Kolodieiev/perfect_console/resources/images/pcb/fact_full.jpg

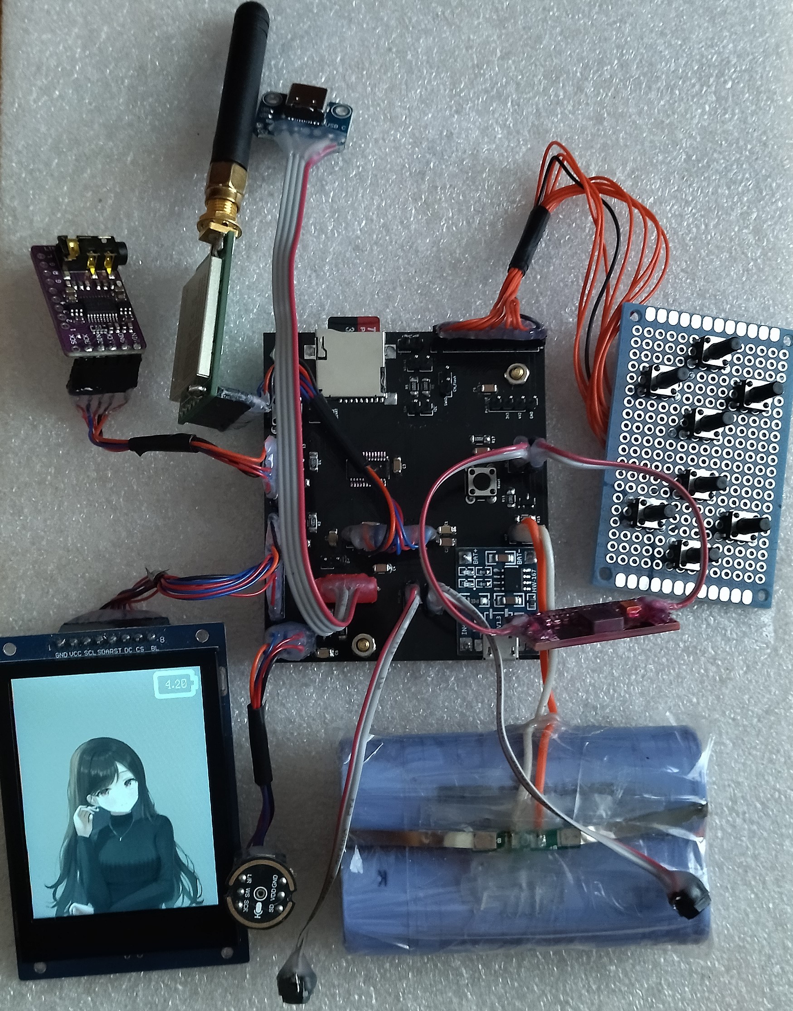
resources/images/pcb/fact_full.jpg
