Kolodieiev/perfect_console/resources/images/pcb/fact_min.jpg

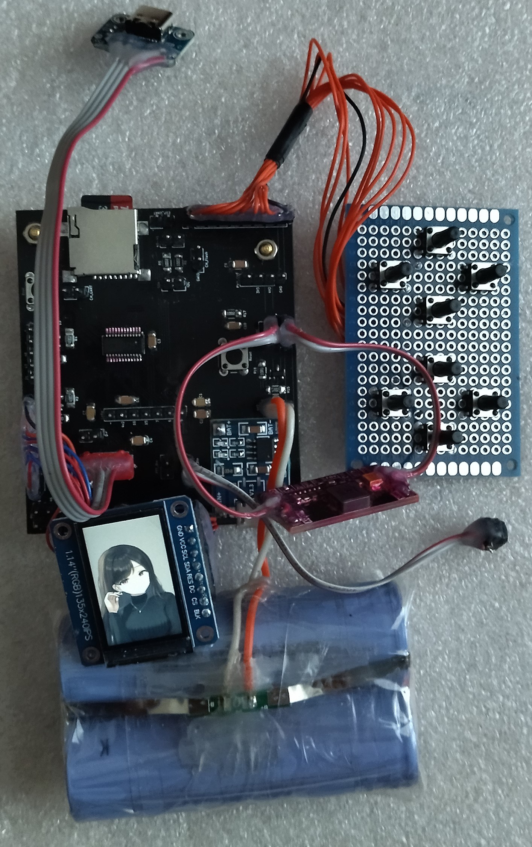
resources/images/pcb/fact_min.jpg
