Kolodieiev/perfect_console/resources/images/pcb/lpt.jpg

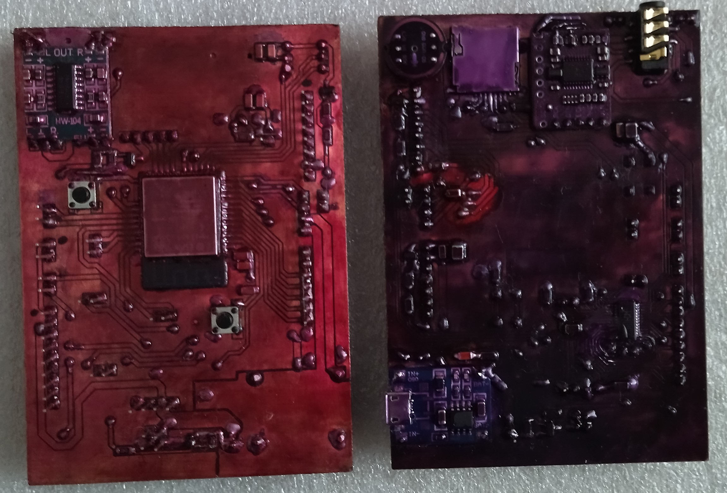
resources/images/pcb/lpt.jpg
