Kolodieiev/perfect_console/firmware/esp32s3_fw/src/pixeler/src/driver/graphics/DisplayWrapper.cpp

#pragma GCC optimize("O3")
#include "DisplayWrapper.h"

#include <esp32-hal-ledc.h>

#include <cmath>

#include "pixeler/src/manager/res/BmpLoader.h"

namespace pixeler
{
  DisplayWrapper::DisplayWrapper()
  {
  }

  DisplayWrapper::~DisplayWrapper()
  {
    log_e("Цього не повинно було статися!");
    esp_restart();
  }

  void DisplayWrapper::fillScreen(uint16_t color)
  {
#ifdef GRAPHICS_ENABLED
#ifdef DIRECT_DRAWING
    _output->fillScreen(color);
#else
    _canvas.fillScreen(color);
    _is_buff_changed = true;
#endif  // #ifdef DIRECT_DRAWING
#endif  // #ifdef GRAPHICS_ENABLED
  }

  void DisplayWrapper::setCursor(int16_t x, int16_t y)
  {
#ifdef GRAPHICS_ENABLED
#ifdef DIRECT_DRAWING
    _output->setCursor(x, y);
#else
    _canvas.setCursor(x, y);
#endif  // #ifdef DIRECT_DRAWING
#endif  // #ifdef GRAPHICS_ENABLED
  }

  void DisplayWrapper::setTextWrap(bool state)
  {
#ifdef GRAPHICS_ENABLED
#ifdef DIRECT_DRAWING
    _output->setTextWrap(state);
#else
    _canvas.setTextWrap(state);
#endif  // #ifdef DIRECT_DRAWING
#endif  // #ifdef GRAPHICS_ENABLED
  }

  void DisplayWrapper::setTextBound(int16_t x, int16_t y, int16_t w, int16_t h)
  {
#ifdef GRAPHICS_ENABLED
#ifdef DIRECT_DRAWING
    return _output->setTextBound(x, y, w, h);
#else
    _is_buff_changed = true;
    return _canvas.setTextBound(x, y, w, h);
#endif  // #ifdef DIRECT_DRAWING
#endif  // #ifdef GRAPHICS_ENABLED
  }

  void DisplayWrapper::resetTextBound()
  {
#ifdef GRAPHICS_ENABLED
#ifdef DIRECT_DRAWING
    return _output->resetTextBound();
#else
    _is_buff_changed = true;
    return _canvas.resetTextBound();
#endif  // #ifdef DIRECT_DRAWING
#endif  // #ifdef GRAPHICS_ENABLED
  }

  size_t DisplayWrapper::print(const char* str)
  {
#ifdef GRAPHICS_ENABLED
#ifdef DIRECT_DRAWING
    return _output->print(str);
#else
    _is_buff_changed = true;
    return _canvas.print(str);
#endif  // #ifdef DIRECT_DRAWING
#else   // not def GRAPHICS_ENABLED
    return 0;
#endif  // #ifdef GRAPHICS_ENABLED
  }

  void DisplayWrapper::setPPAState(bool state)
  {
#ifdef GRAPHICS_ENABLED
    _canvas.setPPAState(state);
#endif  // #ifdef GRAPHICS_ENABLED
  }

  bool DisplayWrapper::isPPAEnabled() const
  {
#ifdef GRAPHICS_ENABLED
    return _canvas.isPPAEnabled();
#else
    return false;
#endif  // #ifdef GRAPHICS_ENABLED
  }

  void DisplayWrapper::setFont(const uint8_t* font)
  {
#ifdef GRAPHICS_ENABLED
#ifdef DIRECT_DRAWING
    _output->setFont(font);
#else
    _canvas.setFont(font);
#endif  // #ifdef DIRECT_DRAWING
#endif  // #ifdef GRAPHICS_ENABLED
  }

  void DisplayWrapper::setTextSize(uint8_t size)
  {
#ifdef GRAPHICS_ENABLED
#ifdef DIRECT_DRAWING
    _output->setTextSize(size, size, 0);
#else
    _canvas.setTextSize(size, size, 0);
#endif  // #ifdef DIRECT_DRAWING
#endif  // #ifdef GRAPHICS_ENABLED
  }

  void DisplayWrapper::setTextColor(uint16_t color)
  {
#ifdef GRAPHICS_ENABLED
#ifdef DIRECT_DRAWING
    _output->setTextColor(color);
#else
    _canvas.setTextColor(color);
#endif  // #ifdef DIRECT_DRAWING
#endif  // #ifdef GRAPHICS_ENABLED
  }

  void DisplayWrapper::calcTextBounds(const char* str, int16_t x, int16_t y, int16_t& x_out, int16_t& y_out, uint16_t& w_out, uint16_t& h_out)
  {
#ifdef GRAPHICS_ENABLED
#ifdef DIRECT_DRAWING
    _output->getTextBounds(str, x, y, x_out, y_out, w_out, h_out);
#else
    _canvas.getTextBounds(str, x, y, x_out, y_out, w_out, h_out);
#endif  // #ifdef DIRECT_DRAWING
#endif  // #ifdef GRAPHICS_ENABLED
  }

  void DisplayWrapper::drawPixel(int16_t x, int16_t y, uint16_t color)
  {
#ifdef GRAPHICS_ENABLED
#ifdef DIRECT_DRAWING
    _output->drawPixel(x, y, color);
#else
    _canvas.drawPixel(x, y, color);
    _is_buff_changed = true;
#endif  // #ifdef DIRECT_DRAWING
#endif  // #ifdef GRAPHICS_ENABLED
  }

  void DisplayWrapper::drawLine(int16_t x0, int16_t y0, int16_t x1, int16_t y1, uint16_t color)
  {
#ifdef GRAPHICS_ENABLED
#ifdef DIRECT_DRAWING
    _output->drawLine(x0, y0, x1, y1, color);
#else
    _canvas.drawLine(x0, y0, x1, y1, color);
    _is_buff_changed = true;
#endif  // #ifdef DIRECT_DRAWING
#endif  // #ifdef GRAPHICS_ENABLED
  }

  void DisplayWrapper::drawCircle(int16_t x, int16_t y, int16_t r, uint16_t color)
  {
#ifdef GRAPHICS_ENABLED
#ifdef DIRECT_DRAWING
    _output->drawCircle(x, y, r, color);
#else
    _canvas.drawCircle(x, y, r, color);
    _is_buff_changed = true;
#endif  // #ifdef DIRECT_DRAWING
#endif  // #ifdef GRAPHICS_ENABLED
  }

  void DisplayWrapper::fillCircle(int16_t x, int16_t y, int16_t r, uint16_t color)
  {
#ifdef GRAPHICS_ENABLED
#ifdef DIRECT_DRAWING
    _output->fillCircle(x, y, r, color);
#else
    _canvas.fillCircle(x, y, r, color);
    _is_buff_changed = true;
#endif  // #ifdef DIRECT_DRAWING
#endif  // #ifdef GRAPHICS_ENABLED
  }

  void DisplayWrapper::drawRect(int32_t x, int32_t y, int32_t w, int32_t h, uint16_t color)
  {
#ifdef GRAPHICS_ENABLED
#ifdef DIRECT_DRAWING
    _output->drawRect(x, y, w, h, color);
#else
    _canvas.drawRect(x, y, w, h, color);
    _is_buff_changed = true;
#endif  // #ifdef DIRECT_DRAWING
#endif  // #ifdef GRAPHICS_ENABLED
  }

  void DisplayWrapper::fillRect(int32_t x, int32_t y, int32_t w, int32_t h, uint16_t color)
  {
#ifdef GRAPHICS_ENABLED
#ifdef DIRECT_DRAWING
    _output->fillRect(x, y, w, h, color);
#else
    _canvas.fillRect(x, y, w, h, color);
    _is_buff_changed = true;
#endif  // #ifdef DIRECT_DRAWING
#endif  // #ifdef GRAPHICS_ENABLED
  }

  void DisplayWrapper::drawRoundRect(int32_t x, int32_t y, int32_t w, int32_t h, int32_t radius, uint16_t color)
  {
#ifdef GRAPHICS_ENABLED
#ifdef DIRECT_DRAWING
    _output->drawRoundRect(x, y, w, h, radius, color);
#else
    _canvas.drawRoundRect(x, y, w, h, radius, color);
    _is_buff_changed = true;
#endif  // #ifdef DIRECT_DRAWING
#endif  // #ifdef GRAPHICS_ENABLED
  }

  void DisplayWrapper::fillRoundRect(int32_t x, int32_t y, int32_t w, int32_t h, int32_t radius, uint16_t color)
  {
#ifdef GRAPHICS_ENABLED
#ifdef DIRECT_DRAWING
    _output->fillRoundRect(x, y, w, h, radius, color);
#else
    _canvas.fillRoundRect(x, y, w, h, radius, color);
    _is_buff_changed = true;
#endif  // #ifdef DIRECT_DRAWING
#endif  // #ifdef GRAPHICS_ENABLED
  }

  void DisplayWrapper::drawBitmap(int16_t x, int16_t y, const uint16_t* bitmap, int16_t w, int16_t h)
  {
#ifdef GRAPHICS_ENABLED
#ifdef DIRECT_DRAWING
    _output->draw16bitRGBBitmap(x, y, bitmap, w, h);
#else
    _canvas.draw16bitRGBBitmap(x, y, bitmap, w, h);
    _is_buff_changed = true;
#endif  // #ifdef DIRECT_DRAWING
#endif  // #ifdef GRAPHICS_ENABLED
  }

  void DisplayWrapper::drawBitmapTransp(int16_t x, int16_t y, const uint16_t* bitmap, int16_t w, int16_t h)
  {
#ifdef GRAPHICS_ENABLED
#ifdef DIRECT_DRAWING
    _output->draw16bitRGBBitmapWithTranColor(x, y, bitmap, COLOR_TRANSPARENT, w, h);
#else
    _canvas.draw16bitRGBBitmapWithTranColor(x, y, bitmap, COLOR_TRANSPARENT, w, h);
    _is_buff_changed = true;
#endif  // #ifdef DIRECT_DRAWING
#endif  // #ifdef GRAPHICS_ENABLED
  }

  void DisplayWrapper::drawBitmapRotated(int16_t x, int16_t y, const uint16_t* bitmap, int16_t w, int16_t h, float piv_x, float piv_y, float angle)
  {
#ifdef GRAPHICS_ENABLED
#ifndef DIRECT_DRAWING
    const float rad = angle * (M_PI / 180.0f);
    const float cos_a = cosf(rad);
    const float sin_a = sinf(rad);

    uint16_t* rotated = static_cast<uint16_t*>(ps_malloc(w * h * sizeof(uint16_t)));
    if (!rotated)
    {
      log_e("Memory allocation failed");
      esp_restart();
    }

    for (int i = 0; i < w * h; i++)
      rotated[i] = COLOR_TRANSPARENT;

    for (int16_t dst_y = 0; dst_y < h; dst_y++)
    {
      const float rel_y = static_cast<float>(dst_y) - piv_y + 0.5f;
      const float y_cos = rel_y * cos_a;
      const float y_sin = rel_y * sin_a;

      for (int16_t dst_x = 0; dst_x < w; dst_x++)
      {
        const float rel_x = static_cast<float>(dst_x) - piv_x + 0.5f;

        const int16_t src_x = static_cast<int16_t>(rel_x * cos_a + y_sin + piv_x);
        const int16_t src_y = static_cast<int16_t>(-rel_x * sin_a + y_cos + piv_y);

        if (src_x >= 0 && src_x < w && src_y >= 0 && src_y < h)
          rotated[dst_y * w + dst_x] = bitmap[src_y * w + src_x];
      }
    }

    _canvas.draw16bitRGBBitmapWithTranColor(x, y, rotated, COLOR_TRANSPARENT, w, h);
    delete[] rotated;
#endif  // #ifndef DIRECT_DRAWING
#endif  // #ifdef GRAPHICS_ENABLED
  }

  uint16_t DisplayWrapper::getFontHeight(const uint8_t* font, uint8_t size)
  {
#ifdef GRAPHICS_ENABLED
    int16_t x1, y1;
    uint16_t w, h;
    _display.setTextSize(size);
    _display.setFont(font);
    _display.calcTextBounds("Ґg", 0, 0, x1, y1, w, h);
    return h;
#else   // not def GRAPHICS_ENABLED
    return 0;
#endif  // #ifdef GRAPHICS_ENABLED
  }

  SemaphoreHandle_t DisplayWrapper::getMutex()
  {
#ifdef GRAPHICS_ENABLED
#ifdef DIRECT_DRAWING
    return nullptr;
#else
    return _sync_mutex;
#endif  // #ifdef DIRECT_DRAWING
#else   // not def GRAPHICS_ENABLED
    return nullptr;
#endif  // #ifdef GRAPHICS_ENABLED
  }

  void DisplayWrapper::rotateDisplaySquare(uint16_t x, uint16_t y, uint16_t side_len, RotateAngle angle)
  {
#ifdef GRAPHICS_ENABLED
#ifndef DIRECT_DRAWING
    side_len = std::min<uint16_t>(side_len, std::min(UI_WIDTH, UI_HEIGHT));
    uint16_t* display_buff = static_cast<uint16_t*>(_canvas.getFramebuffer());
    const size_t square_img_size = side_len * side_len * sizeof(uint16_t);

    uint16_t* square_img = static_cast<uint16_t*>(ps_malloc(square_img_size));
    if (!square_img)
    {
      log_e("Memory allocation failed");
      esp_restart();
    }

    const uint16_t canvas_w = _canvas.width();
    const uint16_t canvas_h = _canvas.height();

    for (uint16_t row = 0; row < side_len; row++)
    {
      uint16_t* src_row_ptr = &display_buff[(y + row) * canvas_w + x];
      uint16_t* dst_row_ptr = &square_img[row * side_len];
      memcpy(dst_row_ptr, src_row_ptr, side_len * sizeof(uint16_t));
    }

    bool old_ppa_state = _canvas.isPPAEnabled();
    if (side_len * side_len > PPA_IMG_SIZE_TRIGG)
      _canvas.setPPAState(true);

    switch (angle)
    {
      case ROTATE_ANGLE_90:
        _canvas.drawBitmapToFramebufferRotate1(square_img, side_len, side_len, display_buff, x, y, canvas_w, canvas_h);
        break;
      case ROTATE_ANGLE_180:
        _canvas.drawBitmapToFramebufferRotate2(square_img, side_len, side_len, display_buff, x, y, canvas_w, canvas_h);
        break;
      case ROTATE_ANGLE_270:
        _canvas.drawBitmapToFramebufferRotate3(square_img, side_len, side_len, display_buff, x, y, canvas_w, canvas_h);
        break;
    }
    _canvas.setPPAState(old_ppa_state);
    free(square_img);
#endif  // #ifdef DIRECT_DRAWING
#endif  // #ifdef GRAPHICS_ENABLED
  }

  void DisplayWrapper::__init()
  {
#ifdef GRAPHICS_ENABLED
    if (BUSS_FREQUENCY < 10000000)
    {
      log_e("Встановлено занадто низьку швидкість шини");
      esp_restart();
    }

#ifdef DIRECT_DRAWING
    _output->begin(BUSS_FREQUENCY);
    _output->setUTF8Print(true);
    _output->setTextWrap(false);
#else
    _canvas.begin(BUSS_FREQUENCY);
    _canvas.setUTF8Print(true);
    _canvas.setTextWrap(false);
#endif  // #ifdef DIRECT_DRAWING

#ifdef INVERT_COLORS
    _output->invertDisplay(INVERT_COLORS);
#endif  //  #ifdef INVERT_COLORS

    _output->setRotation(DISPLAY_ROTATION);

#if ROTATE_CANVAS
    _canvas.setRotation(DISPLAY_ROTATION);
#endif  // #if ROTATE_CANVAS

    _sync_mutex = xSemaphoreCreateMutex();

    if (!_sync_mutex)
    {
      log_e("Недостатньо ресурсів для роботи графічного драйвера");
      esp_restart();
    }

#ifdef DOUBLE_BUFFERRING
    BaseType_t result = xTaskCreatePinnedToCore(displayRendererTask, "dRend", 5 * 512, this, 11, nullptr, 0);

    if (result != pdPASS)
    {
      log_e("Недостатньо ресурсів для роботи графічного драйвера");
      esp_restart();
    }
#endif  // DOUBLE_BUFFERRING
#endif  // #ifdef GRAPHICS_ENABLED
  }

#ifdef ENABLE_SCREENSHOTER
  void DisplayWrapper::takeScreenshot()
  {
    _take_screenshot = true;
    _is_buff_changed = true;
  }
#endif  // ENABLE_SCREENSHOTER

#ifdef PIN_DISPLAY_BL
  void DisplayWrapper::enableBackLight()
  {
#ifdef HAS_BL_PWM
    ledcAttach(PIN_DISPLAY_BL, DISPLAY_BL_PWM_FREQ, DISPLAY_BL_PWM_RES);
    ledcWrite(PIN_DISPLAY_BL, _cur_brightness);
#else
    pinMode(PIN_DISPLAY_BL, OUTPUT);
    digitalWrite(PIN_DISPLAY_BL, HIGH);
#endif  // HAS_BL_PWM
  }

  void DisplayWrapper::disableBackLight()
  {
#ifdef HAS_BL_PWM
    ledcDetach(PIN_DISPLAY_BL);
#endif  // HAS_BL_PWM
    digitalWrite(PIN_DISPLAY_BL, LOW);
  }

#ifdef HAS_BL_PWM
  void DisplayWrapper::setBrightness(uint8_t value)
  {
    if (value == 0)
      fillScreen(COLOR_BLACK);

    _cur_brightness = value;
    ledcWrite(PIN_DISPLAY_BL, value);
  }

  uint8_t DisplayWrapper::getBrightness() const
  {
    return _cur_brightness;
  }
#endif  // HAS_BL_PWM
#endif  // PIN_DISPLAY_BL

#ifdef GRAPHICS_ENABLED
#ifndef DIRECT_DRAWING
  void DisplayWrapper::__flush()
  {
    if (_is_buff_changed)
    {
      _is_buff_changed = false;

#ifdef SHOW_FPS
      if (millis() - _frame_timer < 1000)
      {
        ++_temp_frame_counter;
      }
      else
      {
        _frame_counter = _temp_frame_counter + 1;
        _temp_frame_counter = 0;
        _frame_timer = millis();
      }

      String fps_str = String(_frame_counter);

      _canvas.setTextSize(1);
      _canvas.setFont(font_unifont);
      _canvas.setTextColor(COLOR_RED);

      int16_t x{0};
      int16_t y{0};
      int16_t x_out{0};
      int16_t y_out{0};
      uint16_t w{0};
      uint16_t h{0};

      _canvas.getTextBounds(fps_str.c_str(), x, y, x_out, y_out, w, h);
      //
      uint16_t fps_x_pos = _canvas.width() / 2 - w;
      _canvas.fillRect(fps_x_pos - 3, 0, w + 6, h + 9, COLOR_BLACK);
      _canvas.setCursor(fps_x_pos, h + 3);
      _canvas.print(fps_str);
#endif  // SHOW_FPS

      xSemaphoreTake(_sync_mutex, portMAX_DELAY);
#ifdef DOUBLE_BUFFERRING
      _has_frame = true;
      _canvas.duplicateMainBuff();
#else
      _canvas.flushMainBuff();
#endif  // DOUBLE_BUFFERRING
      xSemaphoreGive(_sync_mutex);

#ifdef ENABLE_SCREENSHOTER
      if (_take_screenshot)
        takeScreenshot(this);
#endif  // ENABLE_SCREENSHOTER
    }
  }
#endif  // #ifndef DIRECT_DRAWING
#endif  // #ifdef GRAPHICS_ENABLED

#ifdef DOUBLE_BUFFERRING
  void DisplayWrapper::displayRendererTask(void* params)
  {
    DisplayWrapper& self = *static_cast<DisplayWrapper*>(params);

    while (1)
    {
      if (self._has_frame)
      {
        xSemaphoreTake(self._sync_mutex, portMAX_DELAY);

        self._has_frame = false;
        self._canvas.flushSecondBuff();

        xSemaphoreGive(self._sync_mutex);
      }
      delay(1);
    }
  }
#endif  // DOUBLE_BUFFERRING

#ifdef ENABLE_SCREENSHOTER
  void DisplayWrapper::takeScreenshot(DisplayWrapper* self)
  {
    self->_take_screenshot = false;

    BmpHeader header;
    header.width = self->_canvas.width();
    header.height = self->_canvas.height();

    String path_to_bmp = "/screenshot_";
    path_to_bmp += millis();
    path_to_bmp += ".bmp";

    BmpLoader loader;
    bool res = loader.saveBmp(header,
                              self->_canvas.getFramebuffer(),
                              path_to_bmp.c_str(),
                              true);

    if (res)
      log_i("Скріншот %s успішно збережено", path_to_bmp.c_str());
    else
      log_e("Помилка створення скріншоту");
  }
#endif  // ENABLE_SCREENSHOTER

  DisplayWrapper _display;
}  // namespace pixeler
