Kolodieiev/perfect_console/firmware/esp32s3_fw/src/pixeler/src/manager/WiFiManager.h

/**
 * @file WiFiManager.h
 * @brief Абстракція над бібліотекою WiFi
 * @details Покращує асинхронну взаємодію з модулем WiFi.
 * Зменшує дублювання часто використовуваного коду.
 */

#pragma once
#pragma GCC optimize("O3")
#include <WiFi.h>

#include <vector>

#include "pixeler/src/defines.h"

namespace pixeler
{
  const char STR_ROUTER_NOT_CONNECTED[] = "Не підключено до маршрутизатора";

  typedef std::function<void(void* arg, wl_status_t conn_status)> WiFiConnectDoneHandler;
  typedef std::function<void(void* arg)> WiFiScanDoneHandler;

  class WiFiManager
  {
  public:
    enum WiFiPowerLevel : uint8_t
    {
      WIFI_POWER_MIN = 0,
      WIFI_POWER_MEDIUM,
      WIFI_POWER_MAX,
    };

    /**
     * @brief Запускає асинхронну спробу підключення до точки доступу із заданими параметрами.
     *
     * @param ssid Ім'я точки доступу.
     * @param pwd Пароль точки доступу.
     * @param wifi_chan Канал WiFi.
     * @param autoreconnect Прапор, що вказує, чи потрібно виконувати автоматичну повторну спробу підключення
     * до точки доступу у разі невдачі або втрати з'єднання.
     * @return true - Якщо запуск спроби підключення виконано успішно.
     * @return false - Якщо не вдалося розпочати підключення.
     */
    bool tryConnectTo(const String& ssid, const String& pwd, uint8_t wifi_chan = 1, bool autoreconnect = false);

    /**
     * @brief Створює точку доступу WiFi, до якої можуть приєднуватися WiFi-клієнти.
     *
     * @param ssid Ім'я точки доступу.
     * @param pwd Пароль точки доступу.
     * @param max_connection Максимальна кількість підключень (більше 0, але менше 10).
     * Рекомендується встановлювати менше 5 одночасних підключень.
     * @param wifi_chan Канал WiFi (менше 11).
     * @param is_hidden Якщо true - точку доступу буде створено прихованою.
     * @return true - Якщо точка доступу створена успішно.
     * @return false - Інакше.
     */
    bool createAP(const String& ssid, const String& pwd, uint8_t max_connection = 1, uint8_t wifi_chan = 1, bool is_hidden = false);

    /**
     * @brief Встановлює обробник події, який буде викликано після завершення спроби підключення до точки доступу.
     *
     * @param handler Асинхронний обробник події завершення спроби підключення до точки доступу.
     * @param args Аргументи, що будуть передані обробнику.
     */
    void setConnectDoneHandler(WiFiConnectDoneHandler handler, void* arg);

    /**
     * @brief Встановлює обробник події, який буде викликано після завершення сканування точок WiFi.
     *
     * @param handler Асинхронний обробник події завершення сканування.
     * @param args Аргументи, що будуть передані обробнику.
     */
    void setScanDoneHandler(WiFiScanDoneHandler handler, void* arg);

    /**
     * @brief Налаштовує WiFi модуль та запускає сканування точок доступу.
     *
     * @return true - Якщо сканування було запущено.
     * @return false - Інакше.
     */
    bool startScan();

    /**
     * @brief Наповнює вектор іменами всіх виявлених точок доступу.
     * Після формування вектора, результат сканування очищується.
     *
     */
    void getScanResult(std::vector<String>& out_vector) const;

    /**
     * @brief Очищує результат попереднього сканування точок доступу.
     *
     */
    void clearScanResult();

    /**
     * @brief Встановлює потужність модуля WiFi.
     *
     * @param power_lvl Значення перечислення потужності модуля.
     * WIFI_POWER_MIN == 5 dBm.
     * WIFI_POWER_MEDIUM == 15 dBm.
     * WIFI_POWER_MAX == 19.5 dBm.
     */
    void setPower(WiFiPowerLevel power_lvl);

    /**
     * @brief Повертає логічне значення, яке вказує на те, чи встановлено з'єднання з WiFi.
     *
     * @return true - Якщо з'єднання встановлено.
     * @return false - Інакше.
     */
    bool isConnected() const;

    /**
     * @brief Повертає логічне значення, яке вказує на те, чи активовано точку доступу на пристрої.
     *
     * @return true - Якщо точка доступу активна.
     * @return false - Інакше.
     */
    bool isApEnabled() const;

    /**
     * @brief Повертає назву WiFi-точки доступу, з якою встановлено з'єднання.
     *
     * @return String - SSID точки доступу, якщо з'єднання існує, або порожній рядок, якщо з'єднання відсутнє.
     */
    String getSSID() const;

    /**
     * @brief Відключається від точки доступу, якщо було встановлено з'єднання.
     *
     */
    void disconnect();

    /**
     * @brief Повертає стан модуля WiFi.
     *
     * @return true - Якщо модуль WiFi увімкнено.
     * @return false - Інакше.
     */
    bool isEnabled() const;

    /**
     * @brief Подає сигнал увімкнення на модуль WiFi.
     *
     * @return true - Якщо модуль WiFi було успішно увімкнено.
     * @return false - Інакше.
     */
    bool enable();

    /**
     * @brief Відключається від точки доступу, якщо було встановлено з'єднання, та вимикає модуль WiFi.
     *
     */
    void disable();

    /**
     * @brief Перемикає поточний стан модуля WiFi на протилежний.
     *
     * @return true - Якщо операцію виконано успішно.
     * @return false - Інакше.
     */
    bool toggle();

    /**
     * @brief Повертає IP-адресу пристрою.
     *
     * @return String - IP-адреса пристрою, якщо пристрій знаходиться в мережі.
     * @return Порожній рядок - інакше.
     */
    String getIP();

    /**
     * @brief Повертає стан прапору, який вказує на те, чи зайнятий зараз модуль WiFi асинхронною роботою на кшталт скануваня чи підключення.
     *
     * @return true - Якщо модуль зайнятий.
     * @return false - Інакше.
     */
    bool isBusy() const;

    WiFiManager() {}
    WiFiManager(const WiFiManager&) = delete;
    WiFiManager& operator=(const WiFiManager&) = delete;
    WiFiManager(WiFiManager&&) = delete;
    WiFiManager& operator=(WiFiManager&&) = delete;

  private:
    void callConnDoneHandler();
    void callScanDoneHandler();

    static void onEvent(WiFiEvent_t event);

  private:
    WiFiScanDoneHandler _scan_done_handler{nullptr};
    WiFiConnectDoneHandler _conn_done_handler{nullptr};

    void* _scan_done_handler_arg{nullptr};
    void* _conn_done_handler_arg{nullptr};

    bool _is_busy{false};
  };

  /**
   * @brief Глобальний об'єкт для роботи з модулем WiFi.
   *
   */
  extern WiFiManager _wifi;
}  // namespace pixeler
