Kolodieiev/perfect_console/firmware/esp32s3_fw/src/pixeler/setup/i2s_setup.h

/**
 * @file i2s_setup.h
 * @brief Файл налаштувань шини I2S
 * @details Якщо цифровий мікрофон або звукову карту не підключено, визначення пінів можна залишити як є.
 */

#pragma once
#include <stdint.h>

#if defined(CONFIG_IDF_TARGET_ESP32S3)

// Піни до яких підключено модуль звукової карти.
#define PIN_I2S_OUT_BCLK 21
#define PIN_I2S_OUT_LRC 48
#define PIN_I2S_OUT_DOUT 47

// Піни до яких підключено цифровий мікрофон.
#define PIN_I2S_IN_SCK 3
#define PIN_I2S_IN_WS 46
#define PIN_I2S_IN_SD 9

#else

#define PIN_I2S_OUT_LRC 15
#define PIN_I2S_OUT_DOUT 5
#define PIN_I2S_OUT_BCLK 18

#define PIN_I2S_IN_SD 14
#define PIN_I2S_IN_SCK 27
#define PIN_I2S_IN_WS 26

#endif
