Kolodieiev/perfect_console/firmware/esp32s3_fw/src/context/splash/SplashContext.h

#pragma once
#include <stdint.h>

#include "pixeler/src/context/IContext.h"

using namespace pixeler;

class SplashContext : public IContext
{
public:
  SplashContext();
  virtual ~SplashContext() {};

protected:
  virtual bool loop() override;
  virtual void update() override;
  //
private:
  void addLabel(uint16_t x_pos, uint16_t y_pos, const char* str, uint16_t color);
  void blinkLED();

private:
  unsigned long _start_time;
  uint8_t _widget_id{1};
};
