Kolodieiev/perfect_console/firmware/esp32s3_fw/src/pixeler_setup/i2c_setup.h

/**
 * @file i2c_setup.h
 * @brief Файл налаштувань шини I2C
 * @details
 */

#pragma once
#include <stdint.h>

#define PIN_I2C_SDA (uint8_t)2
#define PIN_I2C_SCL (uint8_t)1
#define PIN_I2C_INT (uint8_t)42  // Пін для двостороннього зв'язку між I2C-пристроями, якщо такий наявний.

#define I2C_AWAIT_TIME_MS (unsigned long)100  // Час очікування відповіді від i2c пристрою
