Kolodieiev/perfect_console/firmware/esp32s3_fw/src/pixeler_setup/sd_setup.h

/**
 * @file sd_setup.h
 * @brief Файл налаштування карти пам'яті
 * @details
 */

#pragma once
#include <stdint.h>

#define SD_SPI_BUS FSPI  // Номер шини SPI

#define SD_PIN_CS 10  // Бібліотека карти пам'яті вимагає реальний пін, навіть у випадку, якщо CS приєдано до землі.
#define SD_PIN_MOSI 14
#define SD_PIN_SCLK 38
#define SD_PIN_MISO 39

#define SD_FREQUENCY 80000000  // Частота шини SPI.
#define SD_MOUNTPOINT "/sd"    // Точка монтування. Не рекомендуєтсья міняти.
#define SD_MAX_FILES 255       // Максимальна кількість одночасно відкритих файлів.
